MakeMagazinDE/Wallbox-Steuerung/eagle pcb/Bestückungsplan.jpg

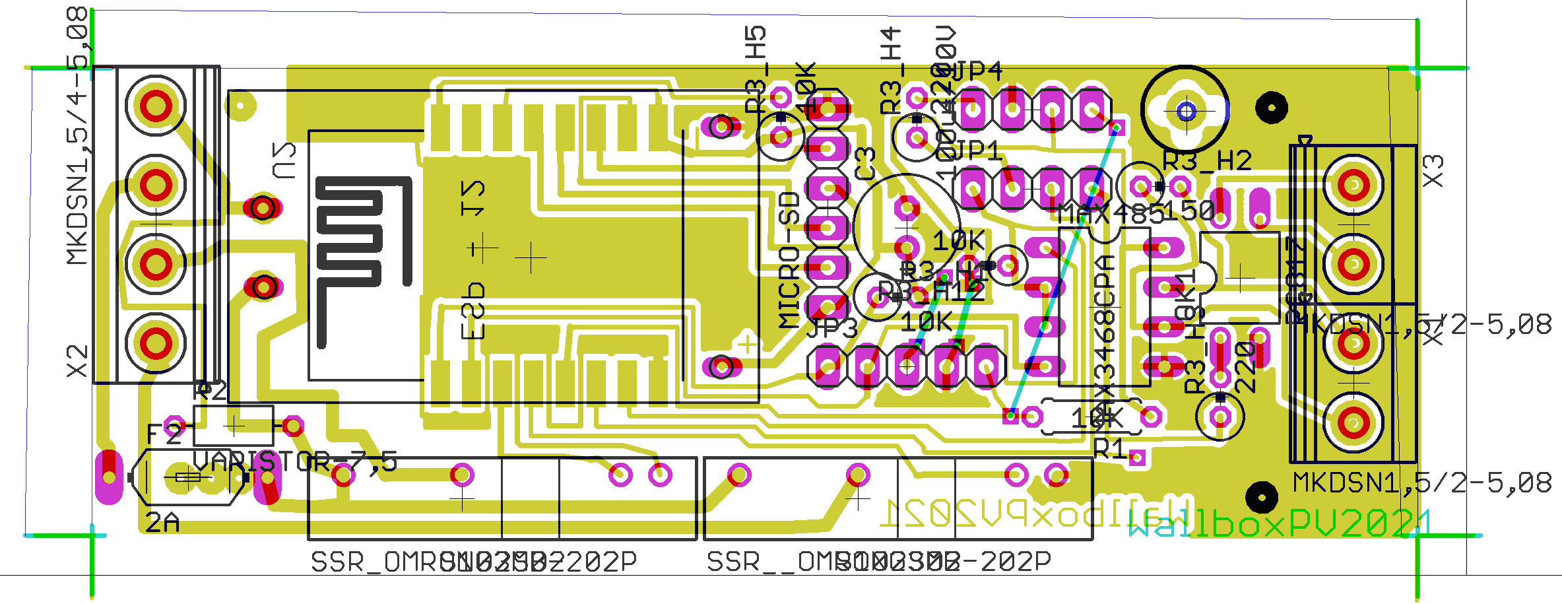
eagle pcb/Bestückungsplan.jpg
