MakeMagazinDE/Wallbox-Steuerung/Wallbox Teil 2/schaltplan.png

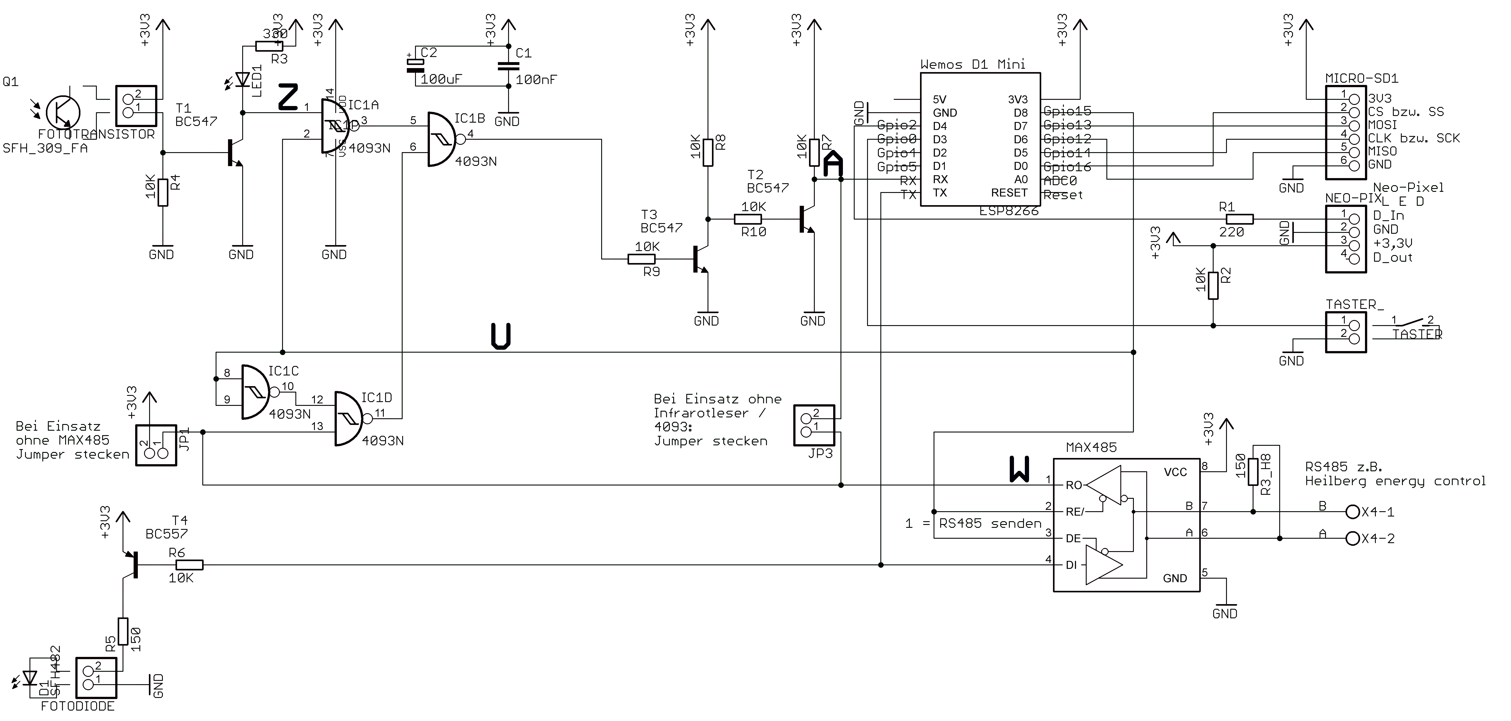
Wallbox Teil 2/schaltplan.png
