MakeMagazinDE/Wallbox-Steuerung/Elektrikerinstallation.JPG

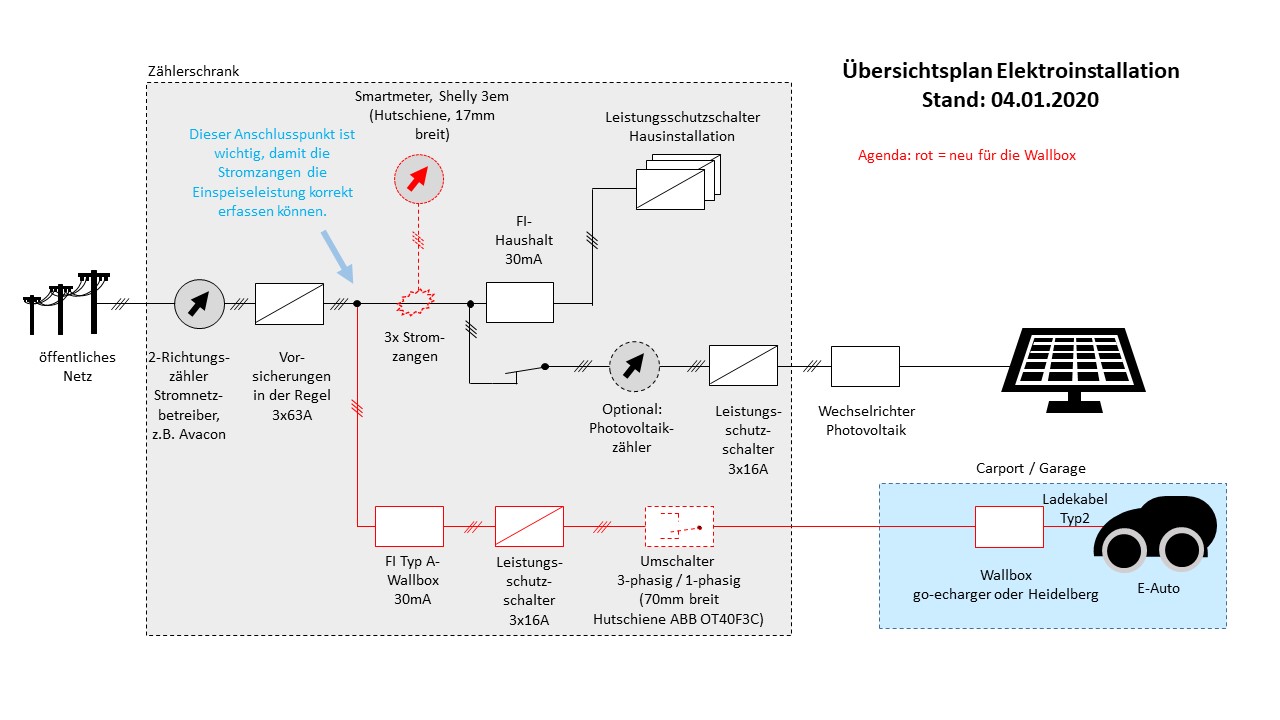
Elektrikerinstallation.JPG
